abetusk/seglow16/img/IMG_20201029_124739.jpg

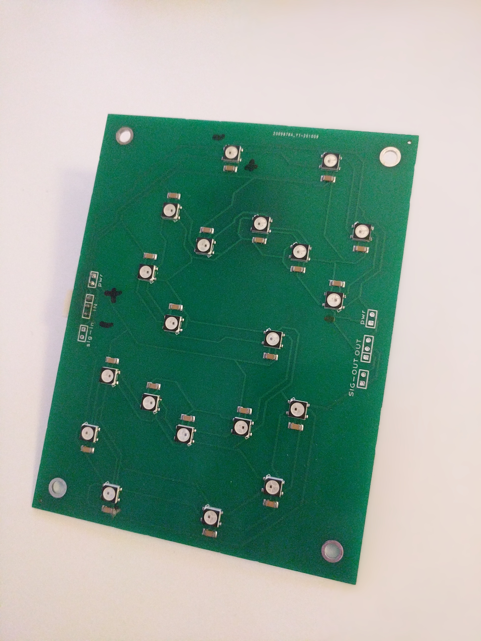
img/IMG_20201029_124739.jpg
